maul1609/laser-sprinting-gates/openSCAD/detector2.stl

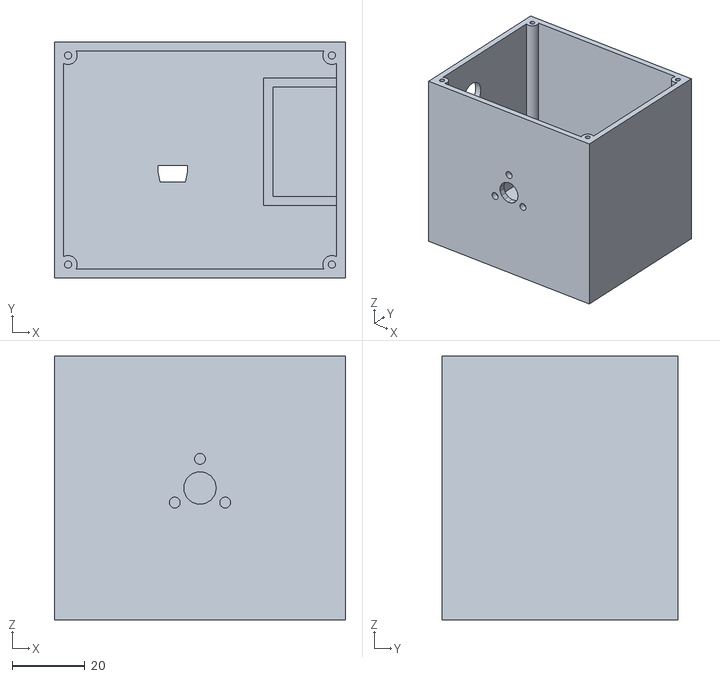
[picture p39: CAD file, 2018-10-22]
openSCAD/detector2.stl
80.0 x 65.0 x 72.5
